tooyipjee/Tracer/images/revB/DSCF9610.JPG

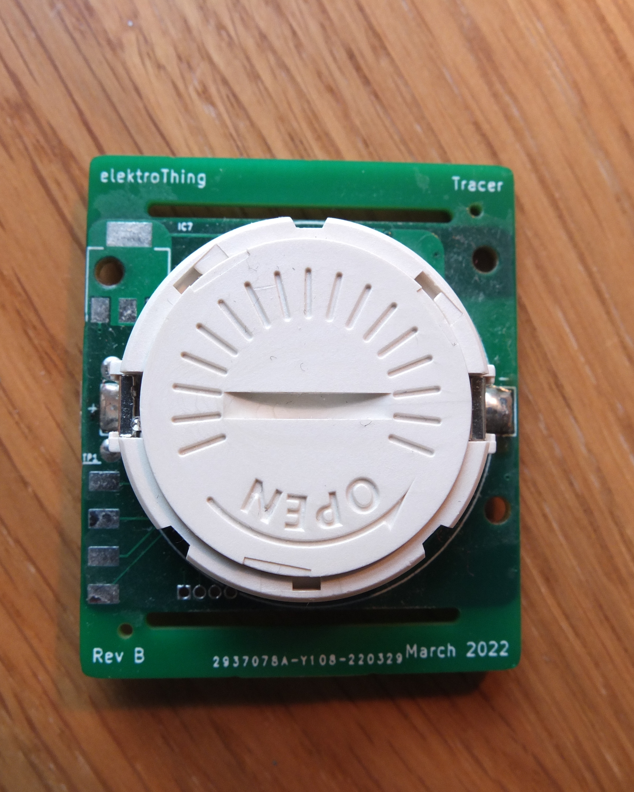
images/revB/DSCF9610.JPG
