tooyipjee/Tracer/pcb/production/Rev F/Docs/Tracer-F_Mask.pdf

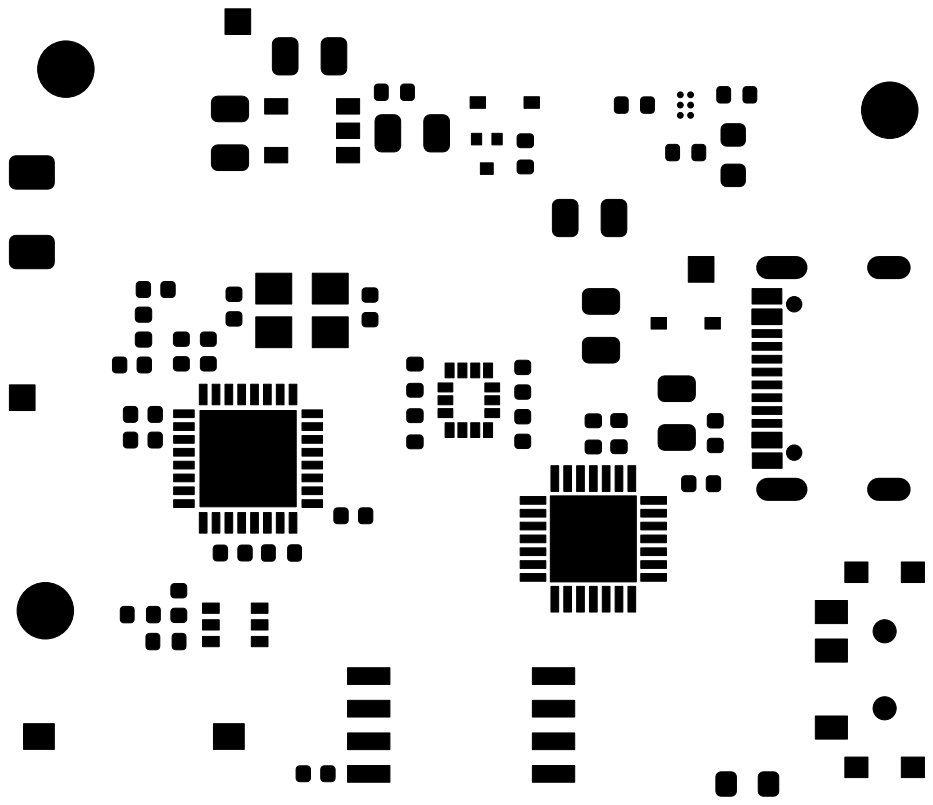
[picture p25: page 1]
