tooyipjee/Tracer/pcb/production/Rev F/Docs/Tracer-F_Paste.pdf

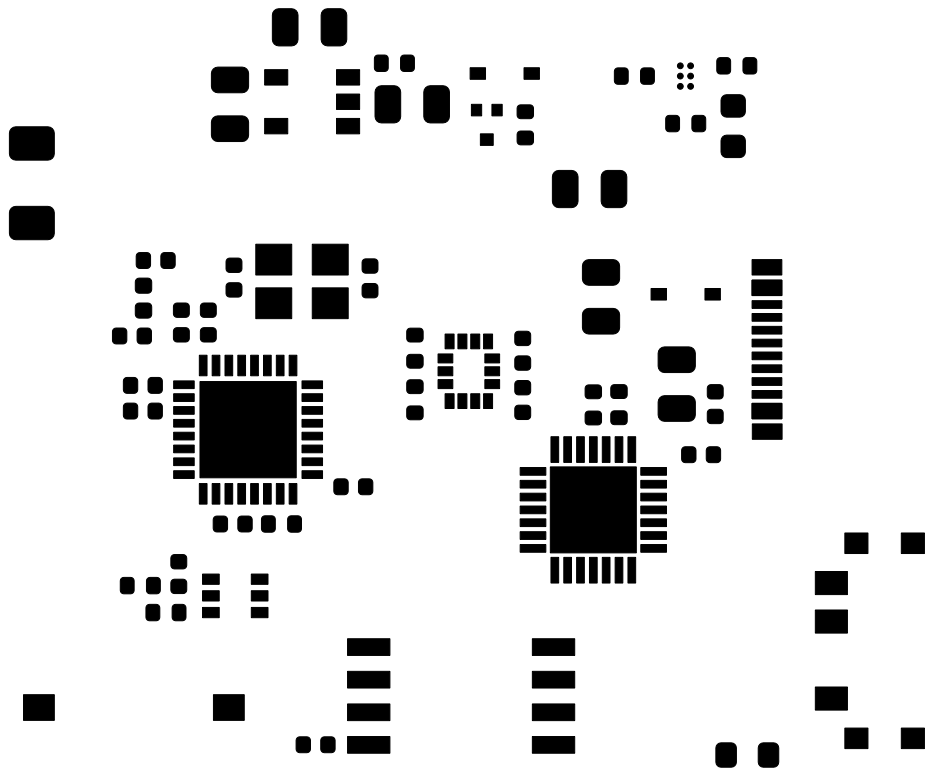
[picture p26: page 1]
