tooyipjee/Tracer/pcb/production/Rev F/Docs/Tracer-F_Silkscreen.pdf

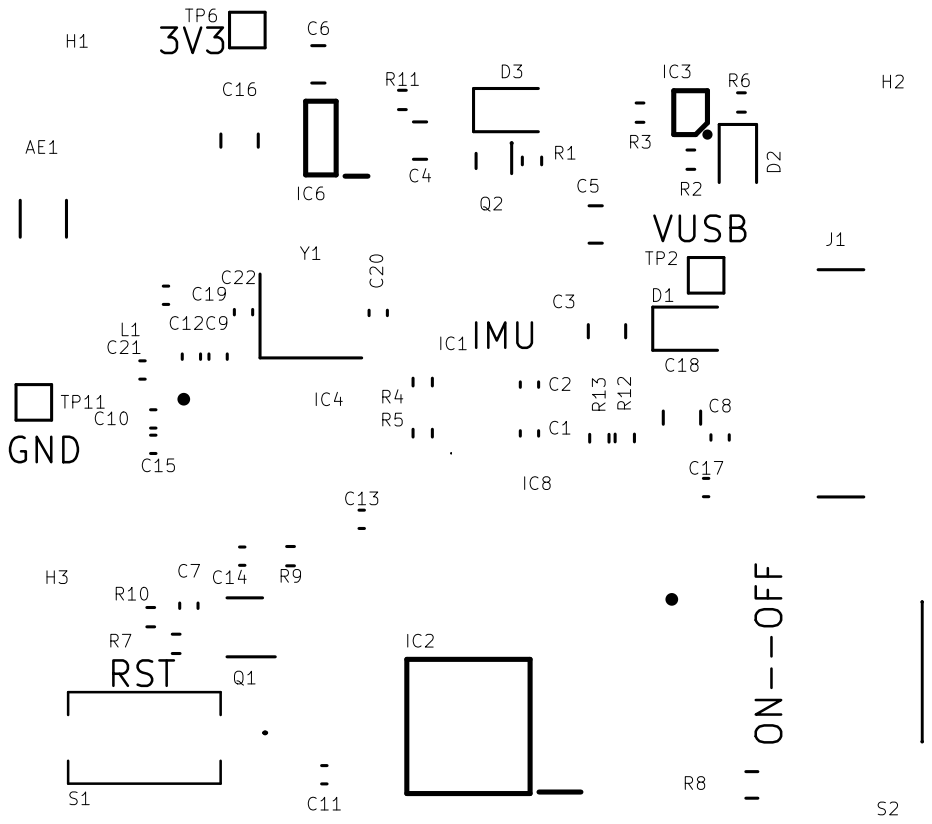
[picture p27: page 1]
