tooyipjee/Tracer/pcb/production/Rev F/Docs/Tracer-In1_Cu.pdf

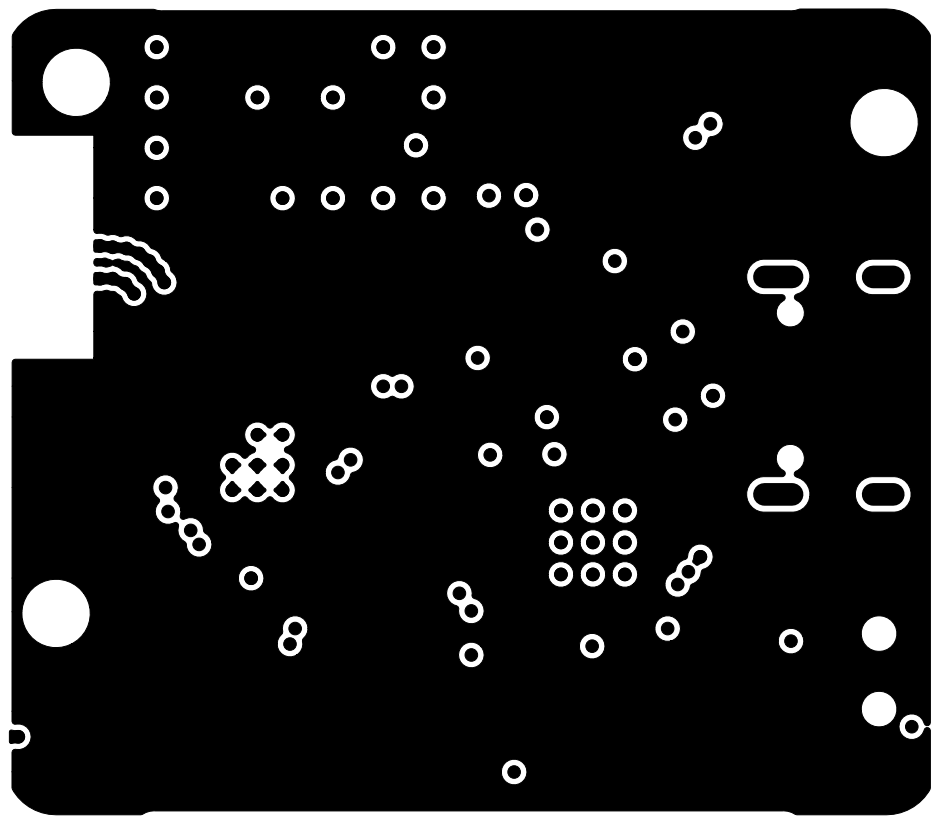
[picture p28: page 1]
