tooyipjee/Tracer/pcb/production/Rev F/Docs/Tracer-In2_Cu.pdf

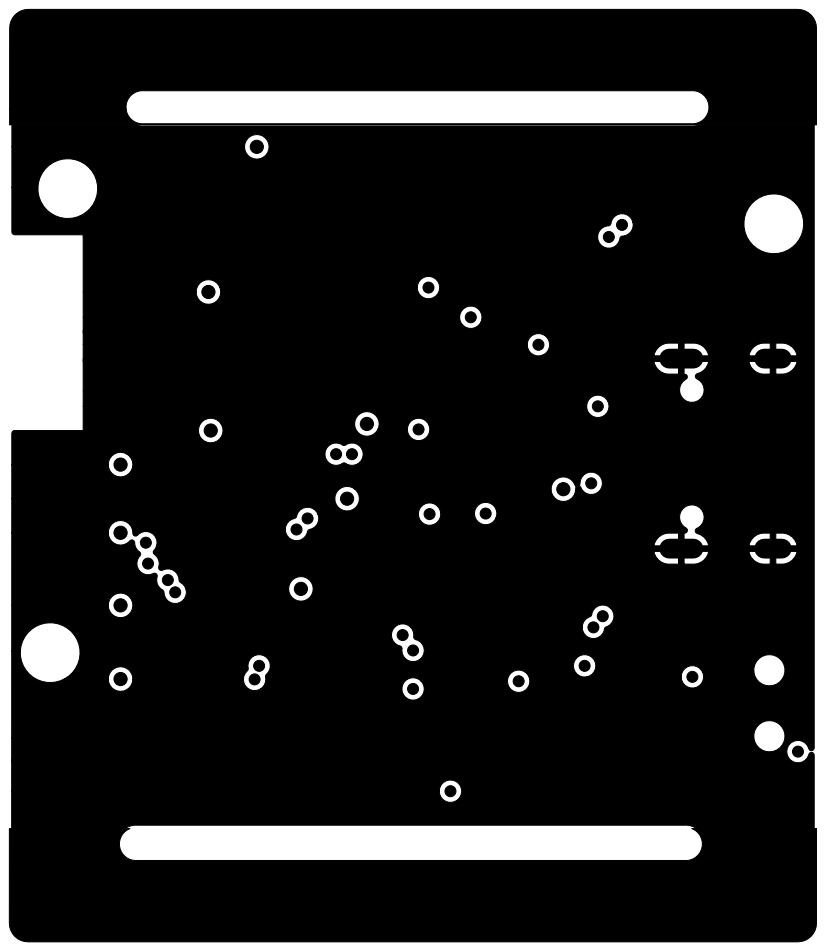
[picture p29: page 1]
